ManiacalLabs/PiPixel/img/9.jpg

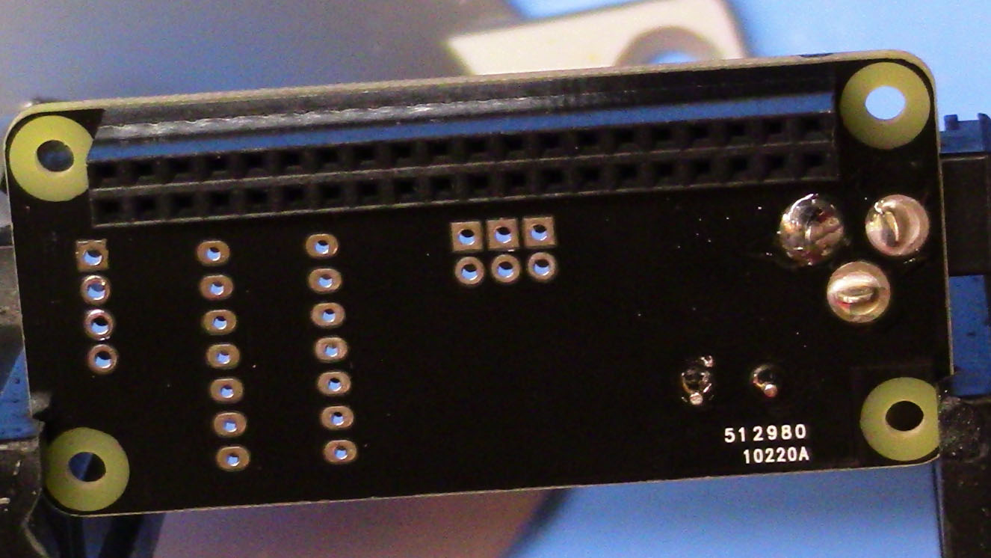
img/9.jpg
